Revers-BR/Anemoia-ESP32/src/controller.h

#ifndef CONTROLLER_H
#define CONTROLLER_H
#include <stdint.h>

enum CONTROLLER
{
    A = (1 << 0), // A Button
    B = (1 << 1), // B Button
    Select = (1 << 2), // Select Button
    Start = (1 << 3), // Start Button
    Up = (1 << 4), // Up Button
    Down = (1 << 5), // Down Button
    Left = (1 << 6), // Left Button
    Right = (1 << 7)  // Right Button
};

void initController();
uint8_t controllerRead();
bool isDownPressed(CONTROLLER button);

uint8_t NESControllerRead();
uint8_t SNESControllerRead();
uint8_t PSXControllerRead();
uint8_t PSXTransferByte(uint8_t byte);

#endif
