Revers-BR/Anemoia-ESP32/src/core/ppu2C02.h

#ifndef PPU2C02_H
#define PPU2C02_H

#include <Arduino.h>
#include <stdint.h>

#include "../../config.h"
#include "cartridge.h"

#define BUFFER_SIZE          (256 + 8 + 8)
#define SCANLINE_SIZE        256
#define SCANLINES_PER_BUFFER 8
#define TILES_PER_SCANLINE   32
#define PIXELS_PER_TILE      8

#ifdef ILI9341_DRIVER
    #undef SCANLINES_PER_BUFFER
    #define SCANLINES_PER_BUFFER 4
#endif

class Bus;
class Ppu2C02
{
public:
    Ppu2C02();
    ~Ppu2C02();

public:
    void ppuWrite(uint16_t addr, uint8_t data);
    uint8_t ppuRead(uint16_t addr);
    void cpuWrite(uint16_t addr, uint8_t data);
    uint8_t cpuRead(uint16_t addr);

    void renderScanline(uint16_t current_scanline);
    void fakeSpriteHit(uint16_t current_scanline);
    void setVBlank();
    void clearVBlank();
    void reset();

    void connectBus(Bus* n)
    {
        bus = n;
    }
    void connectCartridge(Cartridge* cartridge);
    void connectFramebuffer(uint8_t* framebuffer);
    void setMirror(Cartridge::MIRROR mirror);
    Cartridge::MIRROR getMirror();

    void dumpState(File& state);
    void loadState(File& state);

    enum Palette : uint8_t
    {
        NTSC565,
        PAL565,
        NTSC222,
        PAL222,
        PaletteCount
    };
    void setPalette(uint8_t palette);

private:
    Cartridge* cart = nullptr;
    Bus* bus = nullptr;

    void renderBackground();
    void renderSprites();
    void transferScroll();
    void incrementY();
    void finishScanline();
    uint8_t nametable[2048];
    uint8_t* ptr_nametable[4];
    uint8_t palette_table[32];
    uint8_t scanline_counter = 0;
    uint8_t scanline_buffer[BUFFER_SIZE];
    uint8_t scanline_metadata[BUFFER_SIZE];
#ifdef COMPOSITE_VIDEO
    uint8_t* display_buffer = nullptr;
#else
    #ifdef ILI9341_DRIVER
    static uint16_t display_buffer_front[SCANLINE_SIZE * SCANLINES_PER_BUFFER];
    static uint16_t display_buffer_back[SCANLINE_SIZE * SCANLINES_PER_BUFFER];
    #else
    static uint16_t display_buffer[SCANLINE_SIZE * SCANLINES_PER_BUFFER];
    #endif
#endif

    // clang-format off
#ifndef SCREEN_SWAP_BYTES
    static constexpr uint16_t palette_NTSC565[8][64] =
    {
        {
            0x630C, 0x00F2, 0x1835, 0x4013, 0x600D, 0x6804, 0x6020, 0x48E0,
            0x21A0, 0x0240, 0x0260, 0x0242, 0x01AB, 0x0000, 0x0000, 0x0000,
            0xAD55, 0x0A7B, 0x397F, 0x70BE, 0x9857, 0xB08C, 0xA920, 0x8A20,
            0x5320, 0x23E0, 0x0440, 0x0406, 0x0372, 0x0000, 0x0000, 0x0000,
            0xFFFF, 0x553F, 0x843F, 0xB37F, 0xDB1F, 0xFB18, 0xFBAD, 0xDC84,
            0xB560, 0x8640, 0x56A4, 0x3E8D, 0x3E19, 0x4A69, 0x0000, 0x0000,
            0xFFFF, 0xBF1F, 0xCEBF, 0xE65F, 0xF63F, 0xFE3D, 0xFE59, 0xF6B5,
            0xE6F3, 0xD753, 0xC775, 0xB778, 0xB75C, 0xBDD7, 0x0000, 0x0000,
        },
        {
            0x6228, 0x004E, 0x1810, 0x400F, 0x5809, 0x6801, 0x6000, 0x4880,
            0x2140, 0x01A0, 0x01C0, 0x0180, 0x00E7, 0x0000, 0x0000, 0x0000,
            0xAC10, 0x1195, 0x40B9, 0x7018, 0x9812, 0xA828, 0xA0C0, 0x89A0,
            0x5A80, 0x2320, 0x0340, 0x0303, 0x026D, 0x0000, 0x0000, 0x0000,
            0xFE7A, 0x5BFD, 0x831F, 0xB27F, 0xE21C, 0xF233, 0xF2C8, 0xDB80,
            0xB460, 0x8520, 0x5D60, 0x4549, 0x44D4, 0x51A5, 0x0000, 0x0000,
            0xFE7A, 0xC59A, 0xCD3D, 0xE4FD, 0xF4DB, 0xFCD8, 0xFCF4, 0xF550,
            0xE58E, 0xD5EE, 0xC610, 0xBE13, 0xBDF7, 0xBC71, 0x0000, 0x0000,
        },
        {
            0x3AE6, 0x00CE, 0x0010, 0x200E, 0x3808, 0x4800, 0x4020, 0x28E0,
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
            SWAP16(0x5320), SWAP16(0x23E0), SWAP16(0x0440), SWAP16(0x0406), SWAP16(0x0372), SWAP16(0x0000), SWAP16(0x0000), SWAP16(0x0000),
            SWAP16(0xFFFF), SWAP16(0x553F), SWAP16(0x843F), SWAP16(0xB37F), SWAP16(0xDB1F), SWAP16(0xFB18), SWAP16(0xFBAD), SWAP16(0xDC84),
            SWAP16(0xB560), SWAP16(0x8640), SWAP16(0x56A4), SWAP16(0x3E8D), SWAP16(0x3E19), SWAP16(0x4A69), SWAP16(0x0000), SWAP16(0x0000),
            SWAP16(0xFFFF), SWAP16(0xBF1F), SWAP16(0xCEBF), SWAP16(0xE65F), SWAP16(0xF63F), SWAP16(0xFE3D), SWAP16(0xFE59), SWAP16(0xF6B5),
            SWAP16(0xE6F3), SWAP16(0xD753), SWAP16(0xC775), SWAP16(0xB778), SWAP16(0xB75C), SWAP16(0xBDD7), SWAP16(0x0000), SWAP16(0x0000),
        },
        {
            SWAP16(0x6228), SWAP16(0x004E), SWAP16(0x1810), SWAP16(0x400F), SWAP16(0x5809), SWAP16(0x6801), SWAP16(0x6000), SWAP16(0x4880),
            SWAP16(0x2140), SWAP16(0x01A0), SWAP16(0x01C0), SWAP16(0x0180), SWAP16(0x00E7), SWAP16(0x0000), SWAP16(0x0000), SWAP16(0x0000),
            SWAP16(0xAC10), SWAP16(0x1195), SWAP16(0x40B9), SWAP16(0x7018), SWAP16(0x9812), SWAP16(0xA828), SWAP16(0xA0C0), SWAP16(0x89A0),
            SWAP16(0x5A80), SWAP16(0x2320), SWAP16(0x0340), SWAP16(0x0303), SWAP16(0x026D), SWAP16(0x0000), SWAP16(0x0000), SWAP16(0x0000),
            SWAP16(0xFE7A), SWAP16(0x5BFD), SWAP16(0x831F), SWAP16(0xB27F), SWAP16(0xE21C), SWAP16(0xF233), SWAP16(0xF2C8), SWAP16(0xDB80),
            SWAP16(0xB460), SWAP16(0x8520), SWAP16(0x5D60), SWAP16(0x4549), SWAP16(0x44D4), SWAP16(0x51A5), SWAP16(0x0000), SWAP16(0x0000),
            SWAP16(0xFE7A), SWAP16(0xC59A), SWAP16(0xCD3D), SWAP16(0xE4FD), SWAP16(0xF4DB), SWAP16(0xFCD8), SWAP16(0xFCF4), SWAP16(0xF550),
            SWAP16(0xE58E), SWAP16(0xD5EE), SWAP16(0xC610), SWAP16(0xBE13), SWAP16(0xBDF7), SWAP16(0xBC71), SWAP16(0x0000), SWAP16(0x0000),
        },
        {
            SWAP16(0x3AE6), SWAP16(0x00CE), SWAP16(0x0010), SWAP16(0x200E), SWAP16(0x3808), SWAP16(0x4800), SWAP16(0x4020), SWAP16(0x28E0),
            SWAP16(0x09A0), SWAP16(0x0220), SWAP16(0x0260), SWAP16(0x0220), SWAP16(0x0188), SWAP16(0x0000), SWAP16(0x0000), SWAP16(0x0000),
            SWAP16(0x7D0D), SWAP16(0x0235), SWAP16(0x1959), SWAP16(0x4897), SWAP16(0x7050), SWAP16(0x8086), SWAP16(0x7920), SWAP16(0x6220),
            SWAP16(0x3300), SWAP16(0x0BC0), SWAP16(0x0420), SWAP16(0x03E2), SWAP16(0x032D), SWAP16(0x0000), SWAP16(0x0000), SWAP16(0x0000),
            SWAP16(0xC795), SWAP16(0x34DB), SWAP16(0x5BFF), SWAP16(0x8B3F), SWAP16(0xAAD9), SWAP16(0xC2F0), SWAP16(0xC366), SWAP16(0xAC40),
            SWAP16(0x8540), SWAP16(0x5600), SWAP16(0x2E60), SWAP16(0x1E48), SWAP16(0x1DB2), SWAP16(0x2A44), SWAP16(0x0000), SWAP16(0x0000),
            SWAP16(0xC795), SWAP16(0x8E97), SWAP16(0x9E39), SWAP16(0xADF9), SWAP16(0xBDD7), SWAP16(0xC5D4), SWAP16(0xC5F0), SWAP16(0xBE4C),
            SWAP16(0xAEAA), SWAP16(0x9EEA), SWAP16(0x8F0C), SWAP16(0x870F), SWAP16(0x86F3), SWAP16(0x856E), SWAP16(0x0000), SWAP16(0x0000),
        },
        {
            SWAP16(0x4225), SWAP16(0x004C), SWAP16(0x080E), SWAP16(0x280D), SWAP16(0x4007), SWAP16(0x4800), SWAP16(0x4000), SWAP16(0x2880),
            SWAP16(0x0920), SWAP16(0x01A0), SWAP16(0x01C0), SWAP16(0x0160), SWAP16(0x00E7), SWAP16(0x0000), SWAP16(0x0000), SWAP16(0x0000),
            SWAP16(0x840C), SWAP16(0x0194), SWAP16(0x20B7), SWAP16(0x5015), SWAP16(0x700F), SWAP16(0x8025), SWAP16(0x80C0), SWAP16(0x61A0),
            SWAP16(0x3A60), SWAP16(0x0B00), SWAP16(0x0340), SWAP16(0x0302), SWAP16(0x026C), SWAP16(0x0000), SWAP16(0x0000), SWAP16(0x0000),
            SWAP16(0xCE55), SWAP16(0x3BFA), SWAP16(0x631E), SWAP16(0x925D), SWAP16(0xB218), SWAP16(0xCA2F), SWAP16(0xC2A5), SWAP16(0xB380),
            SWAP16(0x8C60), SWAP16(0x5D00), SWAP16(0x3540), SWAP16(0x2527), SWAP16(0x24B1), SWAP16(0x31A3), SWAP16(0x0000), SWAP16(0x0000),
            SWAP16(0xCE55), SWAP16(0x9576), SWAP16(0xA518), SWAP16(0xB4D8), SWAP16(0xC4B7), SWAP16(0xCCB3), SWAP16(0xCCEF), SWAP16(0xC52C),
            SWAP16(0xB58A), SWAP16(0xA5CA), SWAP16(0x95EC), SWAP16(0x8DEF), SWAP16(0x8DD3), SWAP16(0x8C6E), SWAP16(0x0000), SWAP16(0x0000),
        },
        {
            SWAP16(0x4A4F), SWAP16(0x0073), SWAP16(0x1016), SWAP16(0x3014), SWAP16(0x500E), SWAP16(0x5805), SWAP16(0x4800), SWAP16(0x3060),
            SWAP16(0x0900), SWAP16(0x0180), SWAP16(0x01C0), SWAP16(0x0184), SWAP16(0x012D), SWAP16(0x0000), SWAP16(0x0000), SWAP16(0x0000),
            SWAP16(0x8C58), SWAP16(0x01DD), SWAP16(0x30FF), SWAP16(0x603F), SWAP16(0x8018), SWAP16(0x900D), SWAP16(0x88A2), SWAP16(0x6960),
            SWAP16(0x3A40), SWAP16(0x0B00), SWAP16(0x0340), SWAP16(0x0329), SWAP16(0x02B4), SWAP16(0x0001), SWAP16(0x0000), SWAP16(0x0000),
            SWAP16(0xD6BF), SWAP16(0x443F), SWAP16(0x6B5F), SWAP16(0x9ABF), SWAP16(0xC23F), SWAP16(0xD25A), SWAP16(0xD2CF), SWAP16(0xB387),
            SWAP16(0x8C62), SWAP16(0x6522), SWAP16(0x3D88), SWAP16(0x2591), SWAP16(0x2D1C), SWAP16(0x39AC), SWAP16(0x0000), SWAP16(0x0000),
            SWAP16(0xD6BF), SWAP16(0x9DDF), SWAP16(0xA57F), SWAP16(0xBD3F), SWAP16(0xCD1F), SWAP16(0xD51F), SWAP16(0xD53C), SWAP16(0xCD78),
            SWAP16(0xBDD6), SWAP16(0xAE36), SWAP16(0x9E58), SWAP16(0x965B), SWAP16(0x8E3F), SWAP16(0x94B9), SWAP16(0x0000), SWAP16(0x0000),
        },
        {
            SWAP16(0x49E9), SWAP16(0x002E), SWAP16(0x1011), SWAP16(0x300F), SWAP16(0x480A), SWAP16(0x5003), SWAP16(0x4800), SWAP16(0x3040),
            SWAP16(0x08E0), SWAP16(0x0140), SWAP16(0x0160), SWAP16(0x0141), SWAP16(0x00C8), SWAP16(0x0000), SWAP16(0x0000), SWAP16(0x0000),
            SWAP16(0x8BB1), SWAP16(0x0157), SWAP16(0x309A), SWAP16(0x6019), SWAP16(0x8012), SWAP16(0x9009), SWAP16(0x8860), SWAP16(0x6940),
            SWAP16(0x3A20), SWAP16(0x0AA0), SWAP16(0x02E0), SWAP16(0x02C5), SWAP16(0x022F), SWAP16(0x0000), SWAP16(0x0000), SWAP16(0x0000),
            SWAP16(0xD5FB), SWAP16(0x439E), SWAP16(0x6ADF), SWAP16(0x9A1F), SWAP16(0xB9DD), SWAP16(0xD1F4), SWAP16(0xCA6A), SWAP16(0xB322),
            SWAP16(0x8C00), SWAP16(0x64A0), SWAP16(0x3CE3), SWAP16(0x24EC), SWAP16(0x2C76), SWAP16(0x3947), SWAP16(0x0000), SWAP16(0x0000),
            SWAP16(0xD5FB), SWAP16(0x9D1C), SWAP16(0xACDE), SWAP16(0xBC7E), SWAP16(0xCC5C), SWAP16(0xD459), SWAP16(0xD495), SWAP16(0xCCD2),
            SWAP16(0xBD30), SWAP16(0xAD70), SWAP16(0x9D91), SWAP16(0x9595), SWAP16(0x9579), SWAP16(0x9413), SWAP16(0x0000), SWAP16(0x0000),
        },
        {
            SWAP16(0x3A29), SWAP16(0x006F), SWAP16(0x0011), SWAP16(0x200F), SWAP16(0x3809), SWAP16(0x4001), SWAP16(0x3800), SWAP16(0x2060),
            SWAP16(0x0100), SWAP16(0x0180), SWAP16(0x01A0), SWAP16(0x0182), SWAP16(0x0109), SWAP16(0x0000), SWAP16(0x0000), SWAP16(0x0000),
            SWAP16(0x7410), SWAP16(0x01B7), SWAP16(0x18DA), SWAP16(0x4838), SWAP16(0x6811), SWAP16(0x7808), SWAP16(0x70A0), SWAP16(0x5960),
            SWAP16(0x2A40), SWAP16(0x0300), SWAP16(0x0340), SWAP16(0x0325), SWAP16(0x028F), SWAP16(0x0000), SWAP16(0x0000), SWAP16(0x0000),
            SWAP16(0xB679), SWAP16(0x2C1D), SWAP16(0x533F), SWAP16(0x827F), SWAP16(0xA23B), SWAP16(0xBA32), SWAP16(0xBAA9), SWAP16(0xA380),
            SWAP16(0x7C60), SWAP16(0x4D00), SWAP16(0x2D62), SWAP16(0x154B), SWAP16(0x14D5), SWAP16(0x29A7), SWAP16(0x0000), SWAP16(0x0000),
            SWAP16(0xB679), SWAP16(0x859B), SWAP16(0x8D3C), SWAP16(0xA4FC), SWAP16(0xACDB), SWAP16(0xBCD7), SWAP16(0xBCF3), SWAP16(0xB550),
            SWAP16(0xA5AE), SWAP16(0x95EE), SWAP16(0x8610), SWAP16(0x7E13), SWAP16(0x7DD7), SWAP16(0x7C72), SWAP16(0x0000), SWAP16(0x0000),
        },
        {
            SWAP16(0x39E7), SWAP16(0x002D), SWAP16(0x000F), SWAP16(0x200D), SWAP16(0x4008), SWAP16(0x4801), SWAP16(0x4000), SWAP16(0x2840),
            SWAP16(0x08E0), SWAP16(0x0140), SWAP16(0x0160), SWAP16(0x0140), SWAP16(0x00C8), SWAP16(0x0000), SWAP16(0x0000), SWAP16(0x0000),
            SWAP16(0x73AE), SWAP16(0x0155), SWAP16(0x2098), SWAP16(0x4816), SWAP16(0x7010), SWAP16(0x8006), SWAP16(0x7880), SWAP16(0x5940),
            SWAP16(0x3220), SWAP16(0x02C0), SWAP16(0x02E0), SWAP16(0x02C3), SWAP16(0x022D), SWAP16(0x0000), SWAP16(0x0000), SWAP16(0x0000),
            SWAP16(0xBDF7), SWAP16(0x339B), SWAP16(0x5ADF), SWAP16(0x8A1F), SWAP16(0xA9D9), SWAP16(0xB9F1), SWAP16(0xBA67), SWAP16(0xA320),
            SWAP16(0x7C00), SWAP16(0x54A0), SWAP16(0x2D01), SWAP16(0x1CEA), SWAP16(0x1C53), SWAP16(0x2965), SWAP16(0x0000), SWAP16(0x0000),
            SWAP16(0xBDF7), SWAP16(0x8518), SWAP16(0x94BA), SWAP16(0xA47A), SWAP16(0xB459), SWAP16(0xBC55), SWAP16(0xBC91), SWAP16(0xB4CE),
            SWAP16(0xA52C), SWAP16(0x956C), SWAP16(0x858E), SWAP16(0x7D91), SWAP16(0x7D55), SWAP16(0x8410), SWAP16(0x0000), SWAP16(0x0000),
        },
    };

    static constexpr uint16_t palette_NTSC222[8][64] =
    {
        {
            SWAP16(0x52AA), SWAP16(0x0015), SWAP16(0x0015), SWAP16(0x5015), SWAP16(0x500A), SWAP16(0x5000), SWAP16(0x5000), SWAP16(0x5000),
            SWAP16(0x0000), SWAP16(0x02A0), SWAP16(0x02A0), SWAP16(0x02A0), SWAP16(0x000A), SWAP16(0x0000), SWAP16(0x0000), SWAP16(0x0000),
            SWAP16(0xAD55), SWAP16(0x02BF), SWAP16(0x001F), SWAP16(0x501F), SWAP16(0xA815), SWAP16(0xA80A), SWAP16(0xA800), SWAP16(0xAAA0),
            SWAP16(0x52A0), SWAP16(0x02A0), SWAP16(0x0540), SWAP16(0x0540), SWAP16(0x02B5), SWAP16(0x0000), SWAP16(0x0000), SWAP16(0x0000),
            SWAP16(0xFFFF), SWAP16(0x555F), SWAP16(0xAD5F), SWAP16(0xAABF), SWAP16(0xFABF), SWAP16(0xFABF), SWAP16(0xFAAA), SWAP16(0xFD40),
            SWAP16(0xAD40), SWAP16(0xAFE0), SWAP16(0x57E0), SWAP16(0x07EA), SWAP16(0x07FF), SWAP16(0x52AA), SWAP16(0x0000), SWAP16(0x0000),
            SWAP16(0xFFFF), SWAP16(0xAFFF), SWAP16(0xFFFF), SWAP16(0xFFFF), SWAP16(0xFFFF), SWAP16(0xFFFF), SWAP16(0xFFFF), SWAP16(0xFFF5),
            SWAP16(0xFFF5), SWAP16(0xFFF5), SWAP16(0xFFF5), SWAP16(0xAFFF), SWAP16(0xAFFF), SWAP16(0xAD55), SWAP16(0x0000), SWAP16(0x0000),
        },
        {
            SWAP16(0x52AA), SWAP16(0x000A), SWAP16(0x0015), SWAP16(0x500A), SWAP16(0x500A), SWAP16(0x5000), SWAP16(0x5000), SWAP16(0x5000),
            SWAP16(0x0000), SWAP16(0x0000), SWAP16(0x0000), SWAP16(0x0000), SWAP16(0x0000), SWAP16(0x0000), SWAP16(0x0000), SWAP16(0x0000),
            SWAP16(0xAD55), SWAP16(0x0015), SWAP16(0x501F), SWAP16(0x501F), SWAP16(0xA815), SWAP16(0xA80A), SWAP16(0xA800), SWAP16(0xA800),
            SWAP16(0x52A0), SWAP16(0x02A0), SWAP16(0x02A0), SWAP16(0x02A0), SWAP16(0x02AA), SWAP16(0x0000), SWAP16(0x0000), SWAP16(0x0000),
            SWAP16(0xFFFF), SWAP16(0x52BF), SWAP16(0xAABF), SWAP16(0xAABF), SWAP16(0xFABF), SWAP16(0xFAB5), SWAP16(0xFAAA), SWAP16(0xFAA0),
            SWAP16(0xAD40), SWAP16(0xAD40), SWAP16(0x5540), SWAP16(0x554A), SWAP16(0x5555), SWAP16(0x5000), SWAP16(0x0000), SWAP16(0x0000),
            SWAP16(0xFFFF), SWAP16(0xFD5F), SWAP16(0xFD5F), SWAP16(0xFD5F), SWAP16(0xFD5F), SWAP16(0xFD5F), SWAP16(0xFD55), SWAP16(0xFD55),
            SWAP16(0xFD4A), SWAP16(0xFD4A), SWAP16(0xFFF5), SWAP16(0xAFF5), SWAP16(0xAD55), SWAP16(0xAD55), SWAP16(0x0000), SWAP16(0x0000),
        },
        {
            SWAP16(0x02A0), SWAP16(0x000A), SWAP16(0x0015), SWAP16(0x000A), SWAP16(0x000A), SWAP16(0x5000), SWAP16(0x5000), SWAP16(0x0000),
            SWAP16(0x0000), SWAP16(0x02A0), SWAP16(0x02A0), SWAP16(0x02A0), SWAP16(0x000A), SWAP16(0x0000), SWAP16(0x0000), SWAP16(0x0000),
            SWAP16(0x554A), SWAP16(0x02B5), SWAP16(0x001F), SWAP16(0x5015), SWAP16(0x5015), SWAP16(0xA800), SWAP16(0x5000), SWAP16(0x52A0),
            SWAP16(0x02A0), SWAP16(0x02A0), SWAP16(0x0540), SWAP16(0x02A0), SWAP16(0x02AA), SWAP16(0x0000), SWAP16(0x0000), SWAP16(0x0000),
            SWAP16(0xFFF5), SWAP16(0x055F), SWAP16(0x52BF), SWAP16(0xAABF), SWAP16(0xAABF), SWAP16(0xFAB5), SWAP16(0xFAA0), SWAP16(0xAD40),
            SWAP16(0xAD40), SWAP16(0x57E0), SWAP16(0x07E0), SWAP16(0x07EA), SWAP16(0x0555), SWAP16(0x02A0), SWAP16(0x0000), SWAP16(0x0000),
            SWAP16(0xFFF5), SWAP16(0xAFF5), SWAP16(0xAFFF), SWAP16(0xAD5F), SWAP16(0xAD55), SWAP16(0xFD55), SWAP16(0xFD55), SWAP16(0xAFEA),
            SWAP16(0xAFEA), SWAP16(0xAFEA), SWAP16(0xAFEA), SWAP16(0xAFEA), SWAP16(0xAFF5), SWAP16(0xAD4A), SWAP16(0x0000), SWAP16(0x0000),
        },
        {
            SWAP16(0x52A0), SWAP16(0x000A), SWAP16(0x000A), SWAP16(0x000A), SWAP16(0x5000), SWAP16(0x5000), SWAP16(0x5000), SWAP16(0x0000),
            SWAP16(0x0000), SWAP16(0x0000), SWAP16(0x0000), SWAP16(0x0000), SWAP16(0x0000), SWAP16(0x0000), SWAP16(0x0000), SWAP16(0x0000),
            SWAP16(0xAD4A), SWAP16(0x0015), SWAP16(0x0015), SWAP16(0x5015), SWAP16(0x500A), SWAP16(0xA800), SWAP16(0xA800), SWAP16(0x5000),
            SWAP16(0x02A0), SWAP16(0x02A0), SWAP16(0x02A0), SWAP16(0x02A0), SWAP16(0x02AA), SWAP16(0x0000), SWAP16(0x0000), SWAP16(0x0000),
            SWAP16(0xFFF5), SWAP16(0x02BF), SWAP16(0x52BF), SWAP16(0xAABF), SWAP16(0xAABF), SWAP16(0xFAAA), SWAP16(0xFAA0), SWAP16(0xAAA0),
            SWAP16(0xAD40), SWAP16(0x5540), SWAP16(0x0540), SWAP16(0x0540), SWAP16(0x0555), SWAP16(0x0000), SWAP16(0x0000), SWAP16(0x0000),
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
            SWAP16(0x02A0), SWAP16(0x02A0), SWAP16(0x02A0), SWAP16(0x02A0), SWAP16(0x02AA), SWAP16(0x0000), SWAP16(0x0000), SWAP16(0x0000),
            SWAP16(0xAD55), SWAP16(0x02BF), SWAP16(0x52BF), SWAP16(0xAABF), SWAP16(0xA81F), SWAP16(0xA815), SWAP16(0xAAA0), SWAP16(0xAAA0),
            SWAP16(0x5540), SWAP16(0x5540), SWAP16(0x0540), SWAP16(0x054A), SWAP16(0x0555), SWAP16(0x0000), SWAP16(0x0000), SWAP16(0x0000),
            SWAP16(0xAD55), SWAP16(0xAD5F), SWAP16(0xAD5F), SWAP16(0xAD5F), SWAP16(0xAD5F), SWAP16(0xAD55), SWAP16(0xAD55), SWAP16(0xAD4A),
            SWAP16(0xAD4A), SWAP16(0xAD4A), SWAP16(0xAD4A), SWAP16(0x5555), SWAP16(0x5555), SWAP16(0xAD55), SWAP16(0x0000), SWAP16(0x0000),
        },
    };

    static constexpr uint16_t palette_PAL565[8][64] =
    {
        {
            SWAP16(0x630C), SWAP16(0x010C), SWAP16(0x088F), SWAP16(0x280F), SWAP16(0x400C), SWAP16(0x5006), SWAP16(0x5020), SWAP16(0x40A0),
            SWAP16(0x2920), SWAP16(0x09A0), SWAP16(0x01E0), SWAP16(0x01E0), SWAP16(0x0186), SWAP16(0x0000), SWAP16(0x0000), SWAP16(0x0000),
            SWAP16(0xAD55), SWAP16(0x1295), SWAP16(0x31D9), SWAP16(0x5939), SWAP16(0x78D5), SWAP16(0x90CD), SWAP16(0x9144), SWAP16(0x79E0),
            SWAP16(0x5AA0), SWAP16(0x3340), SWAP16(0x13A0), SWAP16(0x03A4), SWAP16(0x032D), SWAP16(0x0000), SWAP16(0x0000), SWAP16(0x0000),
            SWAP16(0xFFFF), SWAP16(0x651F), SWAP16(0x845F), SWAP16(0xABBF), SWAP16(0xCB5F), SWAP16(0xE377), SWAP16(0xE3CE), SWAP16(0xCC86),
            SWAP16(0xAD42), SWAP16(0x85E2), SWAP16(0x6626), SWAP16(0x4E2E), SWAP16(0x4DB7), SWAP16(0x4A69), SWAP16(0x0000), SWAP16(0x0000),
            SWAP16(0xFFFF), SWAP16(0xC6FF), SWAP16(0xD69F), SWAP16(0xE65F), SWAP16(0xEE3F), SWAP16(0xF65C), SWAP16(0xF679), SWAP16(0xEEB6),
            SWAP16(0xE6F4), SWAP16(0xD734), SWAP16(0xC756), SWAP16(0xBF59), SWAP16(0xBF3C), SWAP16(0xBDD7), SWAP16(0x0000), SWAP16(0x0000),
        },
        {
            SWAP16(0x6248), SWAP16(0x0088), SWAP16(0x080C), SWAP16(0x200C), SWAP16(0x4009), SWAP16(0x4804), SWAP16(0x5000), SWAP16(0x4040),
            SWAP16(0x28C0), SWAP16(0x0920), SWAP16(0x0140), SWAP16(0x0120), SWAP16(0x00E3), SWAP16(0x0000), SWAP16(0x0000), SWAP16(0x0000),
            SWAP16(0xA430), SWAP16(0x11B0), SWAP16(0x3114), SWAP16(0x5094), SWAP16(0x7851), SWAP16(0x886A), SWAP16(0x88C2), SWAP16(0x7960),
            SWAP16(0x5A00), SWAP16(0x3280), SWAP16(0x12C0), SWAP16(0x02A1), SWAP16(0x0249), SWAP16(0x0000), SWAP16(0x0000), SWAP16(0x0000),
            SWAP16(0xF699), SWAP16(0x63F9), SWAP16(0x835E), SWAP16(0xA2BE), SWAP16(0xCA7A), SWAP16(0xDA93), SWAP16(0xDAEA), SWAP16(0xCB83),
            SWAP16(0xAC40), SWAP16(0x84C0), SWAP16(0x6503), SWAP16(0x4D0A), SWAP16(0x4CB2), SWAP16(0x49A6), SWAP16(0x0000), SWAP16(0x0000),
            SWAP16(0xF699), SWAP16(0xBD9A), SWAP16(0xCD5B), SWAP16(0xDD1B), SWAP16(0xE4FA), SWAP16(0xECF7), SWAP16(0xED34), SWAP16(0xE571),
            SWAP16(0xDDAF), SWAP16(0xCDEF), SWAP16(0xBE11), SWAP16(0xBE14), SWAP16(0xBDD7), SWAP16(0xB492), SWAP16(0x0000), SWAP16(0x0000),
        },
        {
            SWAP16(0x42C7), SWAP16(0x00E8), SWAP16(0x004B), SWAP16(0x100A), SWAP16(0x2807), SWAP16(0x3003), SWAP16(0x3800), SWAP16(0x2880),
            SWAP16(0x1900), SWAP16(0x0180), SWAP16(0x01C0), SWAP16(0x01C0), SWAP16(0x0163), SWAP16(0x0000), SWAP16(0x0000), SWAP16(0x0000),
            SWAP16(0x7CEE), SWAP16(0x024F), SWAP16(0x1993), SWAP16(0x38F3), SWAP16(0x58AF), SWAP16(0x68A8), SWAP16(0x6900), SWAP16(0x59C0),
            SWAP16(0x4280), SWAP16(0x1B20), SWAP16(0x0360), SWAP16(0x0361), SWAP16(0x02E9), SWAP16(0x0000), SWAP16(0x0000), SWAP16(0x0000),
            SWAP16(0xCF77), SWAP16(0x44B8), SWAP16(0x5BFB), SWAP16(0x835B), SWAP16(0xA317), SWAP16(0xB310), SWAP16(0xB388), SWAP16(0xA421),
            SWAP16(0x84E0), SWAP16(0x6580), SWAP16(0x45C1), SWAP16(0x2DC8), SWAP16(0x2D51), SWAP16(0x3225), SWAP16(0x0000), SWAP16(0x0000),
            SWAP16(0xCF77), SWAP16(0x9677), SWAP16(0xA639), SWAP16(0xADF9), SWAP16(0xBDD7), SWAP16(0xC5D4), SWAP16(0xC5F1), SWAP16(0xBE2E),
            SWAP16(0xAE6D), SWAP16(0xA6AD), SWAP16(0x96CE), SWAP16(0x8ED1), SWAP16(0x8EB4), SWAP16(0x8D4F), SWAP16(0x0000), SWAP16(0x0000),
        },
        {
            SWAP16(0x4226), SWAP16(0x0067), SWAP16(0x000A), SWAP16(0x100A), SWAP16(0x2807), SWAP16(0x3002), SWAP16(0x3800), SWAP16(0x2820),
            SWAP16(0x18A0), SWAP16(0x0100), SWAP16(0x0120), SWAP16(0x0120), SWAP16(0x00C2), SWAP16(0x0000), SWAP16(0x0000), SWAP16(0x0000),
            SWAP16(0x840D), SWAP16(0x01AE), SWAP16(0x1911), SWAP16(0x3891), SWAP16(0x584E), SWAP16(0x6847), SWAP16(0x68A0), SWAP16(0x5940),
            SWAP16(0x41E0), SWAP16(0x2260), SWAP16(0x02A0), SWAP16(0x02A0), SWAP16(0x0228), SWAP16(0x0000), SWAP16(0x0000), SWAP16(0x0000),
            SWAP16(0xCE56), SWAP16(0x43D6), SWAP16(0x633A), SWAP16(0x82BA), SWAP16(0xA256), SWAP16(0xB270), SWAP16(0xB2C8), SWAP16(0xA361),
            SWAP16(0x8400), SWAP16(0x64A0), SWAP16(0x44E1), SWAP16(0x34C8), SWAP16(0x346F), SWAP16(0x3184), SWAP16(0x0000), SWAP16(0x0000),
            SWAP16(0xCE56), SWAP16(0x9576), SWAP16(0xA518), SWAP16(0xB4F8), SWAP16(0xBCD6), SWAP16(0xC4D3), SWAP16(0xC4F0), SWAP16(0xBD2E),
            SWAP16(0xB56C), SWAP16(0xA5AC), SWAP16(0x95CE), SWAP16(0x8DD0), SWAP16(0x95B3), SWAP16(0x8C6E), SWAP16(0x0000), SWAP16(0x0000),
        },
        {
            SWAP16(0x4A4D), SWAP16(0x00CC), SWAP16(0x004F), SWAP16(0x180F), SWAP16(0x300C), SWAP16(0x3807), SWAP16(0x3801), SWAP16(0x2820),
            SWAP16(0x10A0), SWAP16(0x0100), SWAP16(0x0140), SWAP16(0x0161), SWAP16(0x0127), SWAP16(0x0000), SWAP16(0x0000), SWAP16(0x0000),
            SWAP16(0x8C57), SWAP16(0x0215), SWAP16(0x2159), SWAP16(0x48D9), SWAP16(0x6075), SWAP16(0x706D), SWAP16(0x70C5), SWAP16(0x6140),
            SWAP16(0x41E0), SWAP16(0x2280), SWAP16(0x02E0), SWAP16(0x02E6), SWAP16(0x028E), SWAP16(0x0000), SWAP16(0x0000), SWAP16(0x0000),
            SWAP16(0xD6BF), SWAP16(0x4C3F), SWAP16(0x6B7F), SWAP16(0x8AFF), SWAP16(0xAA9F), SWAP16(0xC298), SWAP16(0xBAF0), SWAP16(0xAB89),
            SWAP16(0x8C45), SWAP16(0x64E5), SWAP16(0x4D29), SWAP16(0x3530), SWAP16(0x3CD8), SWAP16(0x39CA), SWAP16(0x0000), SWAP16(0x0000),
            SWAP16(0xD6BF), SWAP16(0x9DDF), SWAP16(0xAD7F), SWAP16(0xBD3F), SWAP16(0xC53F), SWAP16(0xCD3E), SWAP16(0xCD5B), SWAP16(0xC598),
            SWAP16(0xBDD6), SWAP16(0xAE16), SWAP16(0x9E38), SWAP16(0x9E3B), SWAP16(0x9E1E), SWAP16(0x94B8), SWAP16(0x0000), SWAP16(0x0000),
        },
        {
            SWAP16(0x49E9), SWAP16(0x0069), SWAP16(0x000C), SWAP16(0x180C), SWAP16(0x3009), SWAP16(0x3805), SWAP16(0x3800), SWAP16(0x2800),
            SWAP16(0x1080), SWAP16(0x00C0), SWAP16(0x0100), SWAP16(0x0100), SWAP16(0x00C4), SWAP16(0x0000), SWAP16(0x0000), SWAP16(0x0000),
            SWAP16(0x83B1), SWAP16(0x0190), SWAP16(0x20F4), SWAP16(0x4074), SWAP16(0x6031), SWAP16(0x702A), SWAP16(0x7083), SWAP16(0x5900),
            SWAP16(0x41A0), SWAP16(0x2220), SWAP16(0x0260), SWAP16(0x0262), SWAP16(0x020A), SWAP16(0x0000), SWAP16(0x0000), SWAP16(0x0000),
            SWAP16(0xD5FA), SWAP16(0x4BBA), SWAP16(0x62FE), SWAP16(0x8A7E), SWAP16(0xAA3A), SWAP16(0xBA33), SWAP16(0xBA8B), SWAP16(0xAB25),
            SWAP16(0x8BC1), SWAP16(0x6441), SWAP16(0x4CA5), SWAP16(0x348B), SWAP16(0x3C33), SWAP16(0x3167), SWAP16(0x0000), SWAP16(0x0000),
            SWAP16(0xD5FA), SWAP16(0x9D1B), SWAP16(0xA4DC), SWAP16(0xB49C), SWAP16(0xC47B), SWAP16(0xCC98), SWAP16(0xCCB5), SWAP16(0xC4F2),
            SWAP16(0xB531), SWAP16(0xAD70), SWAP16(0x9D92), SWAP16(0x9575), SWAP16(0x9558), SWAP16(0x9413), SWAP16(0x0000), SWAP16(0x0000),
        },
        {
            SWAP16(0x3A28), SWAP16(0x0089), SWAP16(0x000B), SWAP16(0x100B), SWAP16(0x2008), SWAP16(0x3003), SWAP16(0x3000), SWAP16(0x2020),
            SWAP16(0x1080), SWAP16(0x0100), SWAP16(0x0140), SWAP16(0x0140), SWAP16(0x0104), SWAP16(0x0000), SWAP16(0x0000), SWAP16(0x0000),
            SWAP16(0x7410), SWAP16(0x01D0), SWAP16(0x1133), SWAP16(0x3893), SWAP16(0x504F), SWAP16(0x6049), SWAP16(0x60A2), SWAP16(0x5120),
            SWAP16(0x31E0), SWAP16(0x1260), SWAP16(0x02C0), SWAP16(0x02A2), SWAP16(0x026A), SWAP16(0x0000), SWAP16(0x0000), SWAP16(0x0000),
            SWAP16(0xBE79), SWAP16(0x3BF9), SWAP16(0x5B5D), SWAP16(0x7ABD), SWAP16(0x9279), SWAP16(0xAA72), SWAP16(0xAACA), SWAP16(0x9364),
            SWAP16(0x7C20), SWAP16(0x54A0), SWAP16(0x3CE4), SWAP16(0x2CEB), SWAP16(0x2C92), SWAP16(0x29A6), SWAP16(0x0000), SWAP16(0x0000),
            SWAP16(0xBE79), SWAP16(0x8D79), SWAP16(0x953B), SWAP16(0xA4FB), SWAP16(0xACD9), SWAP16(0xB4F7), SWAP16(0xB513), SWAP16(0xAD51),
            SWAP16(0xA58F), SWAP16(0x95CF), SWAP16(0x8DD1), SWAP16(0x85D3), SWAP16(0x85B7), SWAP16(0x7C71), SWAP16(0x0000), SWAP16(0x0000),
        },
        {
            SWAP16(0x39E7), SWAP16(0x0047), SWAP16(0x000A), SWAP16(0x100A), SWAP16(0x2007), SWAP16(0x3003), SWAP16(0x3000), SWAP16(0x2000),
            SWAP16(0x1060), SWAP16(0x00C0), SWAP16(0x0100), SWAP16(0x0100), SWAP16(0x00C3), SWAP16(0x0000), SWAP16(0x0000), SWAP16(0x0000),
            SWAP16(0x73AE), SWAP16(0x018E), SWAP16(0x18F2), SWAP16(0x3872), SWAP16(0x502E), SWAP16(0x6028), SWAP16(0x6081), SWAP16(0x5100),
            SWAP16(0x39A0), SWAP16(0x1A20), SWAP16(0x0260), SWAP16(0x0261), SWAP16(0x0208), SWAP16(0x0000), SWAP16(0x0000), SWAP16(0x0000),
            SWAP16(0xBDF7), SWAP16(0x3B97), SWAP16(0x5AFB), SWAP16(0x7A7B), SWAP16(0x9A17), SWAP16(0xAA31), SWAP16(0xAA89), SWAP16(0x9B03),
            SWAP16(0x7BC0), SWAP16(0x5C40), SWAP16(0x3C83), SWAP16(0x2C89), SWAP16(0x2C31), SWAP16(0x2965), SWAP16(0x0000), SWAP16(0x0000),
            SWAP16(0xBDF7), SWAP16(0x8D17), SWAP16(0x94D9), SWAP16(0xA499), SWAP16(0xB477), SWAP16(0xB475), SWAP16(0xB492), SWAP16(0xB4CF),
            SWAP16(0xA50E), SWAP16(0x954E), SWAP16(0x8D6F), SWAP16(0x8572), SWAP16(0x8555), SWAP16(0x8410), SWAP16(0x0000), SWAP16(0x0000),
        },
    };

    static constexpr uint16_t palette_PAL222[8][64] =
    {
        {
            SWAP16(0x52AA), SWAP16(0x000A), SWAP16(0x000A), SWAP16(0x000A), SWAP16(0x500A), SWAP16(0x5000), SWAP16(0x5000), SWAP16(0x5000),
            SWAP16(0x0000), SWAP16(0x0000), SWAP16(0x0000), SWAP16(0x0000), SWAP16(0x0000), SWAP16(0x0000), SWAP16(0x0000), SWAP16(0x0000),
            SWAP16(0xAD55), SWAP16(0x02B5), SWAP16(0x001F), SWAP16(0x501F), SWAP16(0x5015), SWAP16(0xA80A), SWAP16(0xA800), SWAP16(0x5000),
            SWAP16(0x52A0), SWAP16(0x02A0), SWAP16(0x02A0), SWAP16(0x02A0), SWAP16(0x02AA), SWAP16(0x0000), SWAP16(0x0000), SWAP16(0x0000),
            SWAP16(0xFFFF), SWAP16(0x555F), SWAP16(0xAD5F), SWAP16(0xAABF), SWAP16(0xFABF), SWAP16(0xFAB5), SWAP16(0xFAAA), SWAP16(0xFD40),
            SWAP16(0xAD40), SWAP16(0xAD40), SWAP16(0x57E0), SWAP16(0x57EA), SWAP16(0x5555), SWAP16(0x52AA), SWAP16(0x0000), SWAP16(0x0000),
            SWAP16(0xFFFF), SWAP16(0xFFFF), SWAP16(0xFFFF), SWAP16(0xFFFF), SWAP16(0xFFFF), SWAP16(0xFFFF), SWAP16(0xFFFF), SWAP16(0xFFF5),
            SWAP16(0xFFF5), SWAP16(0xFFF5), SWAP16(0xFFF5), SWAP16(0xAFFF), SWAP16(0xAFFF), SWAP16(0xAD55), SWAP16(0x0000), SWAP16(0x0000),
        },
        {
            SWAP16(0x52AA), SWAP16(0x000A), SWAP16(0x000A), SWAP16(0x000A), SWAP16(0x500A), SWAP16(0x5000), SWAP16(0x5000), SWAP16(0x5000),
            SWAP16(0x0000), SWAP16(0x0000), SWAP16(0x0000), SWAP16(0x0000), SWAP16(0x0000), SWAP16(0x0000), SWAP16(0x0000), SWAP16(0x0000),
            SWAP16(0xAD55), SWAP16(0x0015), SWAP16(0x0015), SWAP16(0x5015), SWAP16(0x5015), SWAP16(0xA80A), SWAP16(0xA800), SWAP16(0x5000),
            SWAP16(0x52A0), SWAP16(0x02A0), SWAP16(0x02A0), SWAP16(0x02A0), SWAP16(0x02AA), SWAP16(0x0000), SWAP16(0x0000), SWAP16(0x0000),
            SWAP16(0xFFFF), SWAP16(0x52BF), SWAP16(0xAABF), SWAP16(0xAABF), SWAP16(0xFABF), SWAP16(0xFAB5), SWAP16(0xFAAA), SWAP16(0xFAA0),
            SWAP16(0xAD40), SWAP16(0xAD40), SWAP16(0x5540), SWAP16(0x554A), SWAP16(0x5555), SWAP16(0x5000), SWAP16(0x0000), SWAP16(0x0000),
            SWAP16(0xFFFF), SWAP16(0xAD5F), SWAP16(0xFD5F), SWAP16(0xFD5F), SWAP16(0xFD5F), SWAP16(0xFD55), SWAP16(0xFD55), SWAP16(0xFD55),
            SWAP16(0xFD4A), SWAP16(0xFD4A), SWAP16(0xAFF5), SWAP16(0xAFF5), SWAP16(0xAD55), SWAP16(0xAD55), SWAP16(0x0000), SWAP16(0x0000),
        },
        {
            SWAP16(0x52A0), SWAP16(0x000A), SWAP16(0x000A), SWAP16(0x000A), SWAP16(0x0000), SWAP16(0x0000), SWAP16(0x0000), SWAP16(0x0000),
            SWAP16(0x0000), SWAP16(0x0000), SWAP16(0x0000), SWAP16(0x0000), SWAP16(0x0000), SWAP16(0x0000), SWAP16(0x0000), SWAP16(0x0000),
            SWAP16(0x554A), SWAP16(0x02AA), SWAP16(0x0015), SWAP16(0x0015), SWAP16(0x500A), SWAP16(0x500A), SWAP16(0x5000), SWAP16(0x5000),
            SWAP16(0x52A0), SWAP16(0x02A0), SWAP16(0x02A0), SWAP16(0x02A0), SWAP16(0x02AA), SWAP16(0x0000), SWAP16(0x0000), SWAP16(0x0000),
            SWAP16(0xFFF5), SWAP16(0x555F), SWAP16(0x52BF), SWAP16(0xAABF), SWAP16(0xAAB5), SWAP16(0xAAB5), SWAP16(0xAAAA), SWAP16(0xAD40),
            SWAP16(0xAD40), SWAP16(0x5540), SWAP16(0x5540), SWAP16(0x054A), SWAP16(0x0555), SWAP16(0x02A0), SWAP16(0x0000), SWAP16(0x0000),
            SWAP16(0xFFF5), SWAP16(0xAFF5), SWAP16(0xAFFF), SWAP16(0xAD5F), SWAP16(0xAD55), SWAP16(0xFD55), SWAP16(0xFD55), SWAP16(0xAFEA),
            SWAP16(0xAFEA), SWAP16(0xAFEA), SWAP16(0xAFEA), SWAP16(0xAFF5), SWAP16(0xAFF5), SWAP16(0xAD4A), SWAP16(0x0000), SWAP16(0x0000),
        },
        {
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
            SWAP16(0x5540), SWAP16(0x5540), SWAP16(0x0540), SWAP16(0x054A), SWAP16(0x0555), SWAP16(0x0000), SWAP16(0x0000), SWAP16(0x0000),
            SWAP16(0xAFFF), SWAP16(0xAD5F), SWAP16(0xAD5F), SWAP16(0xAD5F), SWAP16(0xAD5F), SWAP16(0xAD55), SWAP16(0xAD55), SWAP16(0xAD55),
            SWAP16(0xAD4A), SWAP16(0xAD4A), SWAP16(0xAD55), SWAP16(0xAD55), SWAP16(0xAD55), SWAP16(0x5555), SWAP16(0x0000), SWAP16(0x0000),
        },
        {
            SWAP16(0x0000), SWAP16(0x0000), SWAP16(0x000A), SWAP16(0x000A), SWAP16(0x0000), SWAP16(0x0000), SWAP16(0x0000), SWAP16(0x0000),
            SWAP16(0x0000), SWAP16(0x0000), SWAP16(0x0000), SWAP16(0x0000), SWAP16(0x0000), SWAP16(0x0000), SWAP16(0x0000), SWAP16(0x0000),
            SWAP16(0x52AA), SWAP16(0x000A), SWAP16(0x0015), SWAP16(0x0015), SWAP16(0x500A), SWAP16(0x500A), SWAP16(0x5000), SWAP16(0x5000),
            SWAP16(0x0000), SWAP16(0x02A0), SWAP16(0x02A0), SWAP16(0x02A0), SWAP16(0x02AA), SWAP16(0x0000), SWAP16(0x0000), SWAP16(0x0000),
            SWAP16(0xAD55), SWAP16(0x02B5), SWAP16(0x52BF), SWAP16(0x52BF), SWAP16(0xAAB5), SWAP16(0xAAB5), SWAP16(0xAAAA), SWAP16(0xAAA0),
            SWAP16(0x52A0), SWAP16(0x5540), SWAP16(0x0540), SWAP16(0x054A), SWAP16(0x0555), SWAP16(0x0000), SWAP16(0x0000), SWAP16(0x0000),
            SWAP16(0xAD55), SWAP16(0xAD55), SWAP16(0xAD5F), SWAP16(0xAD5F), SWAP16(0xAD55), SWAP16(0xAD55), SWAP16(0xAD55), SWAP16(0xAD4A),
            SWAP16(0xAD4A), SWAP16(0xAD4A), SWAP16(0xAD4A), SWAP16(0xAD55), SWAP16(0xAD55), SWAP16(0xAD55), SWAP16(0x0000), SWAP16(0x0000),
        },
    };
    #undef SWAP16
#endif
    // clang-format on

    const uint16_t (*nes_palette)[64] = palette_NTSC565;
    static constexpr uint8_t palette_mirror[32] = {
        0x00, 0x01, 0x02, 0x03, 0x04, 0x05, 0x06, 0x07, 0x08, 0x09, 0x0A,
        0x0B, 0x0C, 0x0D, 0x0E, 0x0F, 0x00, 0x11, 0x12, 0x13, 0x04, 0x15,
        0x16, 0x17, 0x08, 0x19, 0x1A, 0x1B, 0x0C, 0x1D, 0x1E, 0x1F
    };

    // PPU Registers
    // PPUCTRL
    union
    {
        struct
        {
            uint8_t nametable_x : 1;
            uint8_t nametable_y : 1;
            uint8_t VRAM_addr_increment : 1;
            uint8_t sprite_table_addr : 1;
            uint8_t background_table_addr : 1;
            uint8_t sprite_size : 1;
            uint8_t PPU_master_select : 1;
            uint8_t Vblank_NMI : 1;
        };
        uint8_t reg = 0x00;
    } control;

    // PPUMASK
    union
    {
        struct
        {
            uint8_t grayscale : 1;
            uint8_t render_background_left : 1;
            uint8_t render_sprite_left : 1;
            uint8_t render_background : 1;
            uint8_t render_sprite : 1;
            uint8_t emphasize : 3;
        };
        uint8_t reg = 0x00;
    } mask;

    // PPUSTATUS
    union
    {
        struct
        {
            uint8_t unused : 5;
            uint8_t sprite_overflow : 1;
            uint8_t sprite_zero_hit : 1;
            uint8_t VBlank : 1;
        };
        uint8_t reg = 0x00;
    } status;

    // OAMADDR
    uint8_t OAMADDR = 0x00;
    // OAMDATA
    uint8_t OAMDATA = 0x00;

    // Internal register
    typedef union
    {
        struct
        {
            uint16_t coarse_x : 5;
            uint16_t coarse_y : 5;
            uint16_t nametable_x : 1;
            uint16_t nametable_y : 1;
            uint16_t fine_y : 3;
            uint16_t unused : 1;
        };
        uint16_t reg = 0x00;
    } internal_register;

    // OAM
    typedef struct
    {
        uint8_t y;
        uint8_t index;
        uint8_t attribute;
        uint8_t x;
    } OAM;

    OAM sprite[64];
    internal_register v;
    internal_register t;
    uint8_t x;
    uint8_t w;
    uint8_t PPUDATA_buffer = 0x00;

    // Rendering
    uint16_t scanline = 0x00;
    uint8_t* ptr_scanline_meta = nullptr;

public:
    uint8_t* ptr_sprite = (uint8_t*)sprite;
    uint8_t* ptr_buffer = scanline_buffer;
#ifdef COMPOSITE_VIDEO
    uint8_t* ptr_display;
#else
    #ifdef ILI9341_DRIVER
    static uint16_t* ptr_display;
    static uint16_t* ptr_back_buffer;
    #else
    static constexpr uint16_t* ptr_display = display_buffer;
    #endif
#endif
};

#endif
